henrydimaria94-cell/243-4J5-LI/labo/Labo-02/code/lilygo_wifi_mschapv2/lilygo_wifi_mschapv2.ino

#include <WiFi.h>
#include <esp_wpa2.h>
#include "auth.h"

void setup() {
  Serial.begin(115200);

  WiFi.disconnect(true);
  WiFi.mode(WIFI_STA);

  esp_wifi_sta_wpa2_ent_set_identity((uint8_t *)EAP_IDENTITY, strlen(EAP_IDENTITY));
  esp_wifi_sta_wpa2_ent_set_username((uint8_t *)EAP_USERNAME, strlen(EAP_USERNAME));
  esp_wifi_sta_wpa2_ent_set_password((uint8_t *)EAP_PASSWORD, strlen(EAP_PASSWORD));
  esp_wifi_sta_wpa2_ent_enable();

  WiFi.begin(WIFI_SSID);

  Serial.print("Connexion");
  while (WiFi.status() != WL_CONNECTED) {
    delay(500);
    Serial.print(".");
  }

  Serial.println("\nConnecté!");
  Serial.print("IP: ");
  Serial.println(WiFi.localIP());
}

void loop() {

}
