henrydimaria94-cell/243-4J5-LI/labo/Labo-02/code/lilygo_lte_mqtt_toggle/auth.h

// auth.h - Configuration LTE/Cellulaire
#ifndef AUTH_H
#define AUTH_H
// ============================================================================
// CONFIGURATION APN (Access Point Name) - CELLULAIRE
// ============================================================================
// ⚠️ IMPORTANT: Remplacez ces valeurs par celles de votre opérateur cellulaire
//
// Exemples d'APN par opérateur au Canada:
//   - Bell:        "inet.bell.ca" ou "pda.bell.ca"
//   - Rogers:      "internet.com" ou "ltemobile.apn"
//   - Telus:       "sp.telus.com" ou "isp.telus.com"
//   - Fido:        "internet.fido.ca"
//   - Koodo:       "sp.koodo.com"
//   - Virgin:      "media.bell.ca"
//   - Videotron:   "media.videotron"
//
// La plupart des opérateurs canadiens n'exigent pas de username/password
// ============================================================================

const char APN[] = "internet.keepgo.com";      // ⚠️ À remplacer par votre APN
const char APN_USER[] = "";             // Généralement vide au Canada
const char APN_PASS[] = "";             // Généralement vide au Canada

// ============================================================================
// CONFIGURATION MQTT
// ============================================================================

const char MQTT_BROKER[] = "mqtt.henri-dumont.com";
const int  MQTT_PORT = 1883;  // Port standard MQTT (non-SSL via LTE)
const char MQTT_USER[] = "esp_user";
const char MQTT_PASS[] = "Dumont@1994";  // ⚠️ À remplacer par votre mot de passe MQTT

// Device ID - Identifiant unique de l'appareil
// Format suggéré: "esp32-XXXXXX" (6 derniers caractères de l'IMEI ou personnalisé)
// Cet identifiant sera utilisé comme préfixe pour tous les topics MQTT
const char MQTT_CLIENT_ID[] = "esp32-henridumont";     // ⚠️ À personnaliser selon votre appareil

#endif // AUTH_H
